Nana0Nana/N.A.G.E.K.I./pic/IMG_8331.JPG

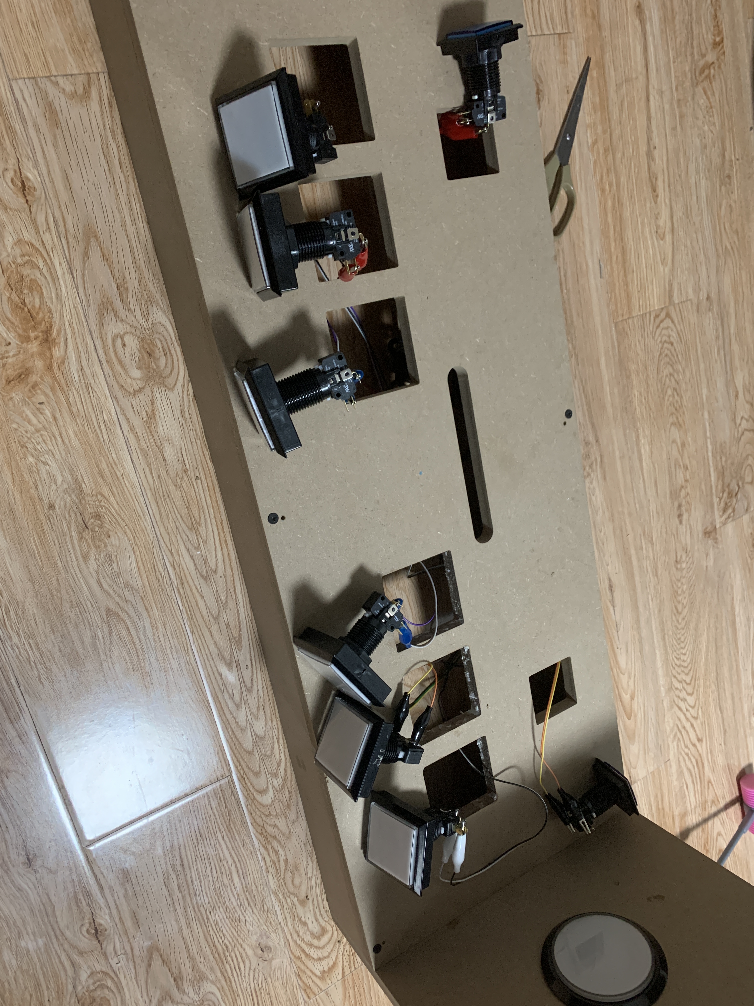
pic/IMG_8331.JPG
